Xing-Zao/Feixue-jujiqiang/00_Priority README/02_source/如何编辑技术文档源文件.pdf

# 如何编辑技术⽂档源⽂

件

# LonlyPan

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
# 如何编辑技术⽂档源⽂件

小书匠软件是没有⼯程⽬录这个概念的，但为了⽂件管理⽅便，我们称 xx.md所在的⽂件夹为⼯程⽂件夹。

⼀个⼯程⽂件夹格式应该如下：

在我们使⽤小书匠新建⽂件并保存时，如果⽂档中使⽤了例如绘图、图⽚等附件，该软件会⾃动在原⽂档的同级⽬ 录下新建各个附件⽂件夹，并保存对应的附件进去。

以上的 attachments，images 都是该软件⾃动建⽴的。

好了说了这么多，结论如下：

在使⽤小书匠为每个项⽬编写技术⽂档时，我们需要⾃⼰单独建⽴⼀个⽂件夹，保存该⽂档。

当要打开并要修改⼀个项⽬的技术⽂档时，我们需要：

1. 单击左上⻆“小书匠”图标
2. 单击“绑定”，单击“本地⽂件存储”

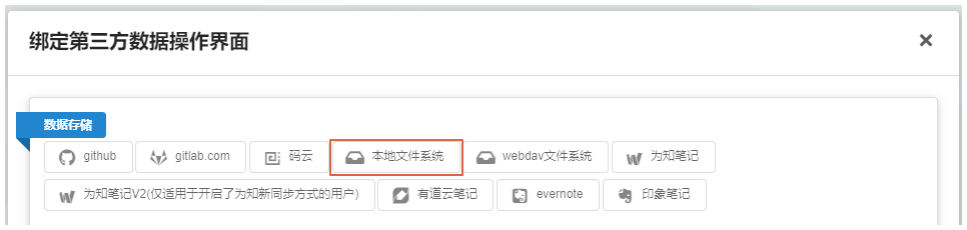
[picture p1: figure]

选中 xxx.md ⽂件所在的⽂件夹，⼀般为每个项⽬下的“00_Priority README”下的“02_source” ⽂件夹。

xxx.项⽬
|______attachments//保存绘图附件
|______images | //保存图⽚附件
|______xxx1.md | //原⽂档1
|______xxx2.md | //原⽂档2

1/3

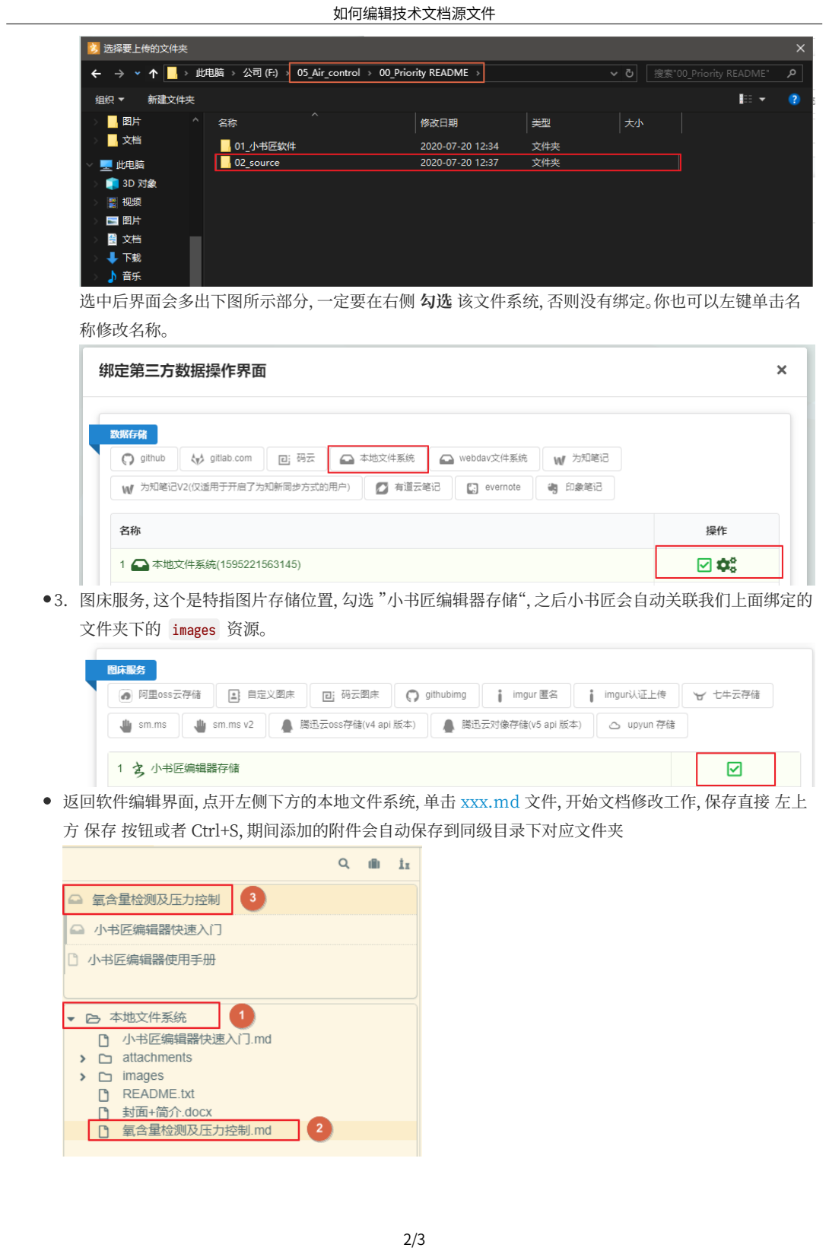
[picture p2: page 4]

选中后界⾯会多出下图所⽰部分，⼀定要在右侧 勾选 该⽂件系统，否则没有绑定。你也可以左键单击名 称修改名称。

3. 图床服务，这个是特指图⽚存储位置，勾选 ”小书匠编辑器存储“，之后小书匠会⾃动关联我们上⾯绑定的 ⽂件夹下的 images资源。

返回软件编辑界⾯，点开左侧下⽅的本地⽂件系统，单击 xxx.md ⽂件，开始⽂档修改⼯作，保存直接 左上 ⽅ 保存 按钮或者 Ctrl+S，期间添加的附件会⾃动保存到同级⽬录下对应⽂件夹

2/3

注意：
之后要想修改每⼀个项⽬的技术⽂档，都需要按照上述步骤 绑定⽂件夹，再打开⽂件修改。 否则修改的⽂件附件会出现在其它⽂件夹下，造成丢失。

3/3
