Xing-Zao/Feixue-jujiqiang/01_Firmware/01_source/01_new_source/jujiqiang-battery-V1.0.0/README.txt

适配 B2.3  电路
用于实际测试使用，存在少许非致命bug，功能和使用没有问题。

ToDo：
    1. 通多读取芯片内部温度，近似知道使用环境温度

版本更新:
   B1.0.0 2020/08/31  
      0. 适配 B1.0  电路
      1. 更改部分I/O接口顺序
      2. 添加代码注释
      3. 优化整体逻辑

    B2.0.0 2020/09/04  
      0. 适配 B2.0  电路
      1. 更改部分I/O接口顺序
      2. 优化整体逻辑

    B2.1.0 2020/09/11  
       0. 适配 B2.0  电路
       1. 修复电池测量bug
       2. 代码重构
       3. 添加报错时的语音提示
       4. 修复充电完成，80-100%指示灯仍闪烁bug
       5. 更改退料时间 23s -> 30s

    B2.1.1 2020/09/22 
       0. 适配 B2.1 电路
       1. 添加边充边用功能
       2. 添加 5% 低电量语音提示一次(不关机)
       3. 修改了温度对照表（电压由 3.3 -> 3V）
       4. 修复开机语音延时1s播报bug
       5. 修改低电量电压对应参数，修复电压时无法工作与退料bug
       6. 修复插入充电头时灯延时2s工作bug
       
    B2.1.2 2020/09/22 
       0. 适配 B2.2 电路
       1. 修改开机语音提示
       2. 修复电池供电无法开机bug
       3. 修复开机加热期间再关机,语音播放不全bug-20201022
       4. 增加看门狗复位，解决边充边用时usb频繁插拔一定机率死机bug-2020102
    BUG：开机键按，红灯闪
       1. 修复温度对照表 = B2.1.0版本之前，电压改变不影响对照表
     [X]单击的判定时间  
     [X]调速键，无语音提示，但调速功能被激活（问题2）
     [X]电量计算增加均值
     [X]故障的判断：增加次数阈值判断
     [X]按开机键红灯闪烁一下，调整初始化顺序，优先初始化
     [X]近充满电状态，按下进料键，会概率性出现“正在充电中语音提示”
               硬件问题，去除 D3 二极管。顺便也解决了问题2
     [X]使用状态下充满电，拔掉充电器，电量始终显示满电bug
        
    B2.2.0 2020/12/02 
       0. 语音芯片改为两线串口
       
    V1.0.0 2021/01/23 
       0. 删除边充边用功能
       1. 修复充电无法检测满电状态bug
       
    V1.0.1 2021/03/24 
       0. 修复温度较低环境下加热报错：提示不能工作了 的bug
       
    V1.0.1.1 2021/04/17(该修复为临时性，新一批电电机需要重新测试)
       0. 修复低速PWM值用以解决当前批次电机低速堵转问题
