Xing-Zao/Feixue-jujiqiang/02_Electronics/01_source/02_old_source/main_V1.1/BOM/15-25M20PPM20PF-30+85℃_2018-07-26.PDF

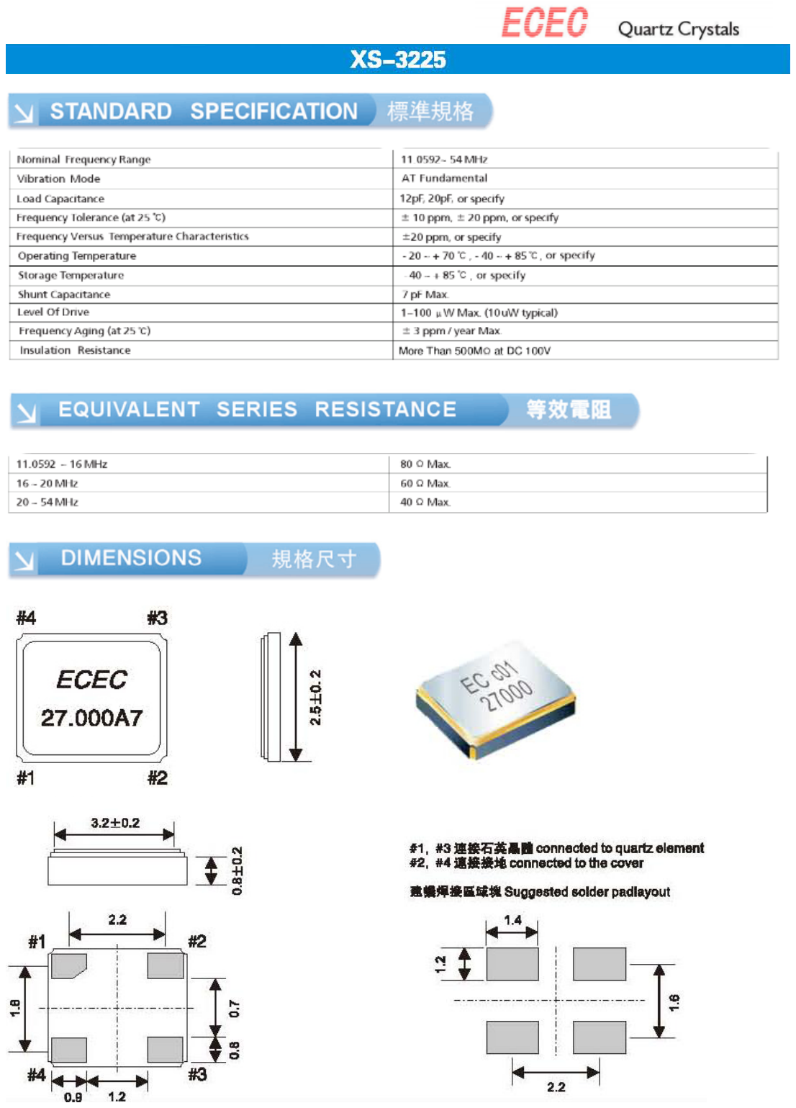
[picture p4: page 1]
