Xing-Zao/Feixue-jujiqiang/02_Electronics/01_source/01_new_source/main_V1.1/Light_detector_V1.0.pdf

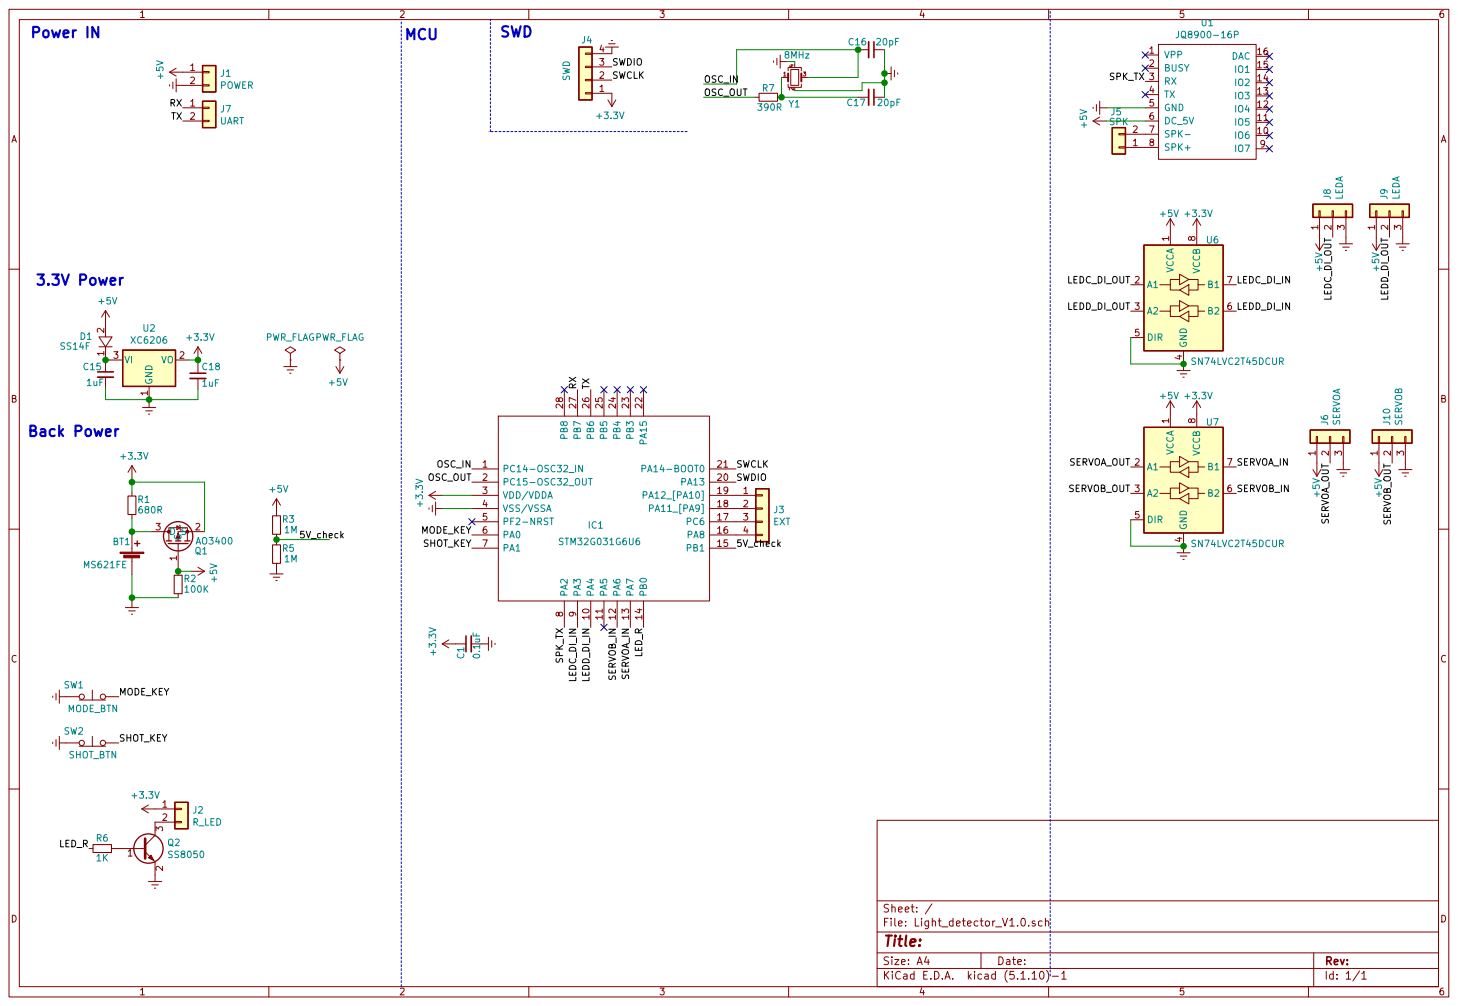
[picture p12: page 1]

File: Light_detector_V1.0.sch Sheet: /
Rev: | D Date: KiCad E.D.A. kicad (5.1.10)-1 Size: A4
