Xing-Zao/Feixue-jujiqiang/02_Electronics/01_source/01_new_source/tiny_V1.0/tiny_V1.0.pdf

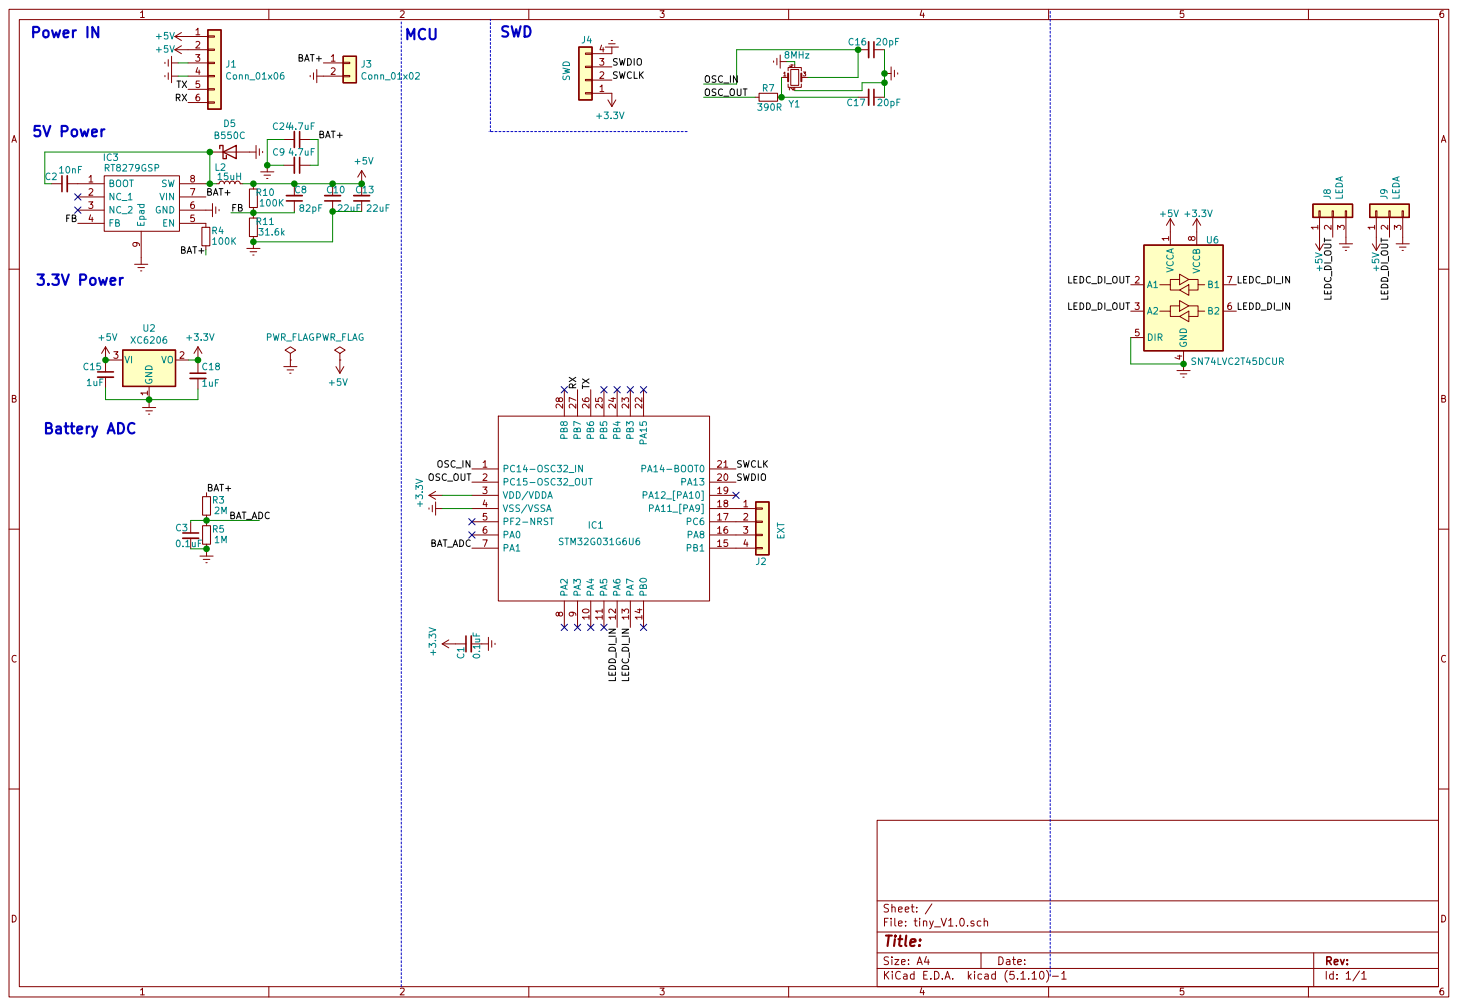
[picture p13: page 1]

3 J8LEDA +5V +3.3V C2 10nF BOOT 1 NC_1 2 NC_2 3 FB 4 EN 5 GND 6 VIN 7 SW 8 Epad

File: tiny_V1.0.sch Sheet: /
Rev: | D Date: KiCad E.D.A. kicad (5.1.10)-1 Size: A4
