Xing-Zao/Feixue-jujiqiang/02_Electronics/01_source/02_old_source/main_V1.1/BOM/16-CL22BK122-16A.pdf

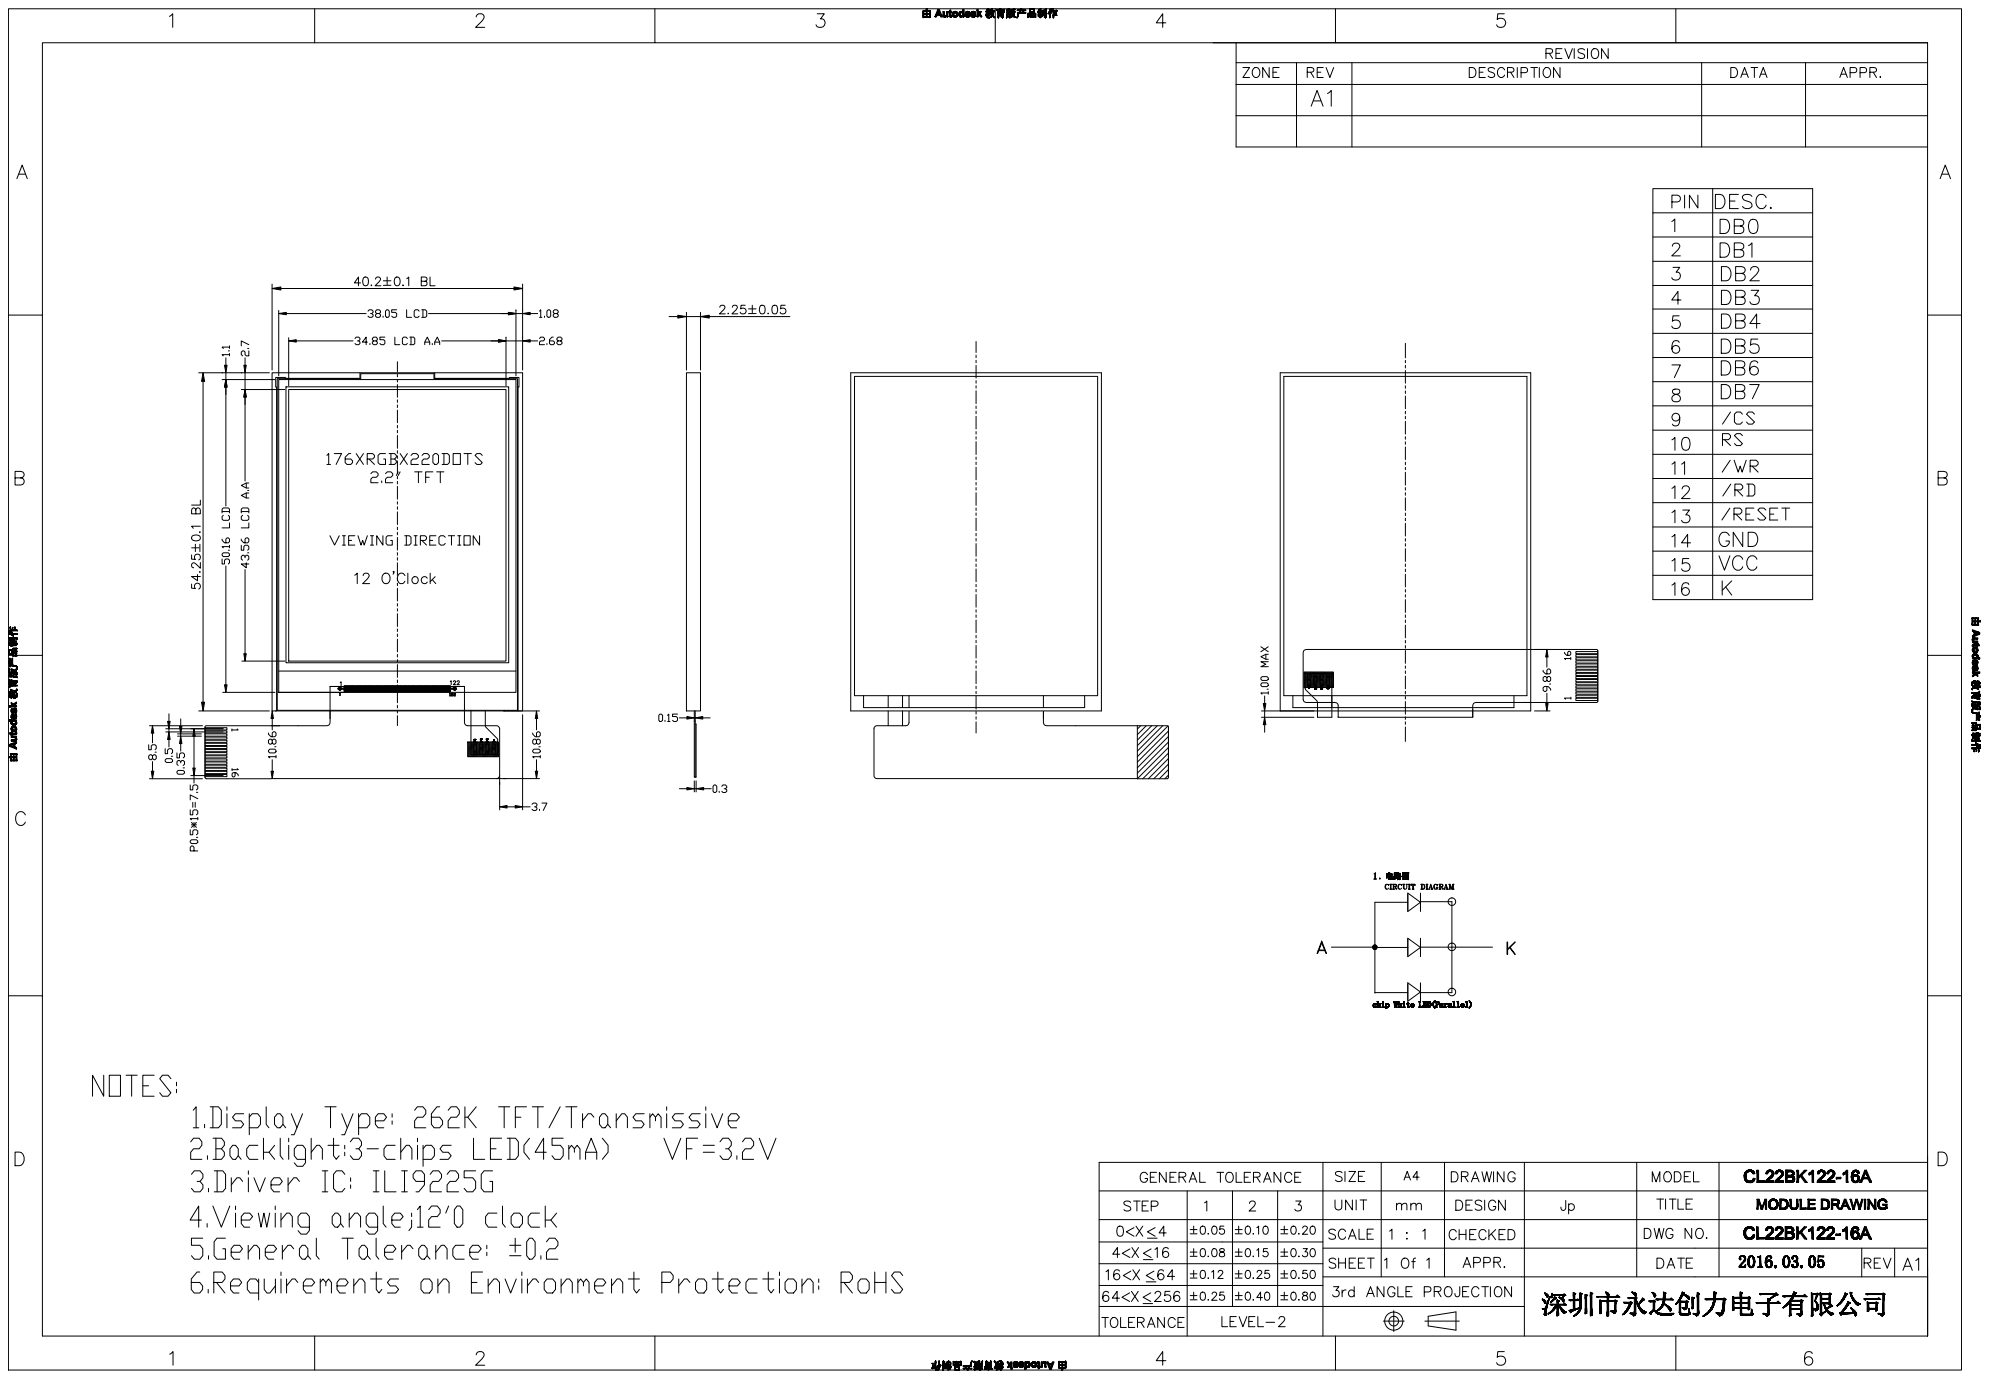
[picture p15: page 1]
