Xing-Zao/Feixue-jujiqiang/01_Firmware/01_source/01_new_source/jujiqiang-main-v1.1.0/Smart1/Configuration.h

/******************** (C) COPYRIGHT  小不点信息科技********************
 * 描 述   ：配置文件
 * 版 本   ：V1.0.1
 * 作 者   ：LonlyPan
* date：   2020-08-19
* Note    ：请在专业人员指导下修改
***********************************************************************/

#ifndef CONFIGURATION_H_
#define CONFIGURATION_H_

#define OPEN_ANGLE 120
#define CLOSE_ANGLE 0


#endif /* CONFIGURATION_H_ */
