Xing-Zao/Feixue-jujiqiang/01_Firmware/01_source/01_new_source/jujiqiang-battery-v1.1.0/Smart1/comHeader.h

/*
 * SmartConfig.h
 *
 *  Created on: Aug 18, 2020
 *      Author: 23714
 */

#ifndef COMHEADER_H_
#define COMHEADER_H_

#include "stm32g0xx_hal.h"
#include "main.h"
#include "stdbool.h"

#include "macros.h"

//#define millis() HAL_GetTick()

#endif /* COMHEADER_H_ */
